BoujeeEnjinia1701/heatmap-node/cad/drawings/HMN-DWG-001.pdf

CONCEPT, NOT FOR FABRICATION | HeatMap Node · github.com/BoujeeEnjinia1701/heatmap-node

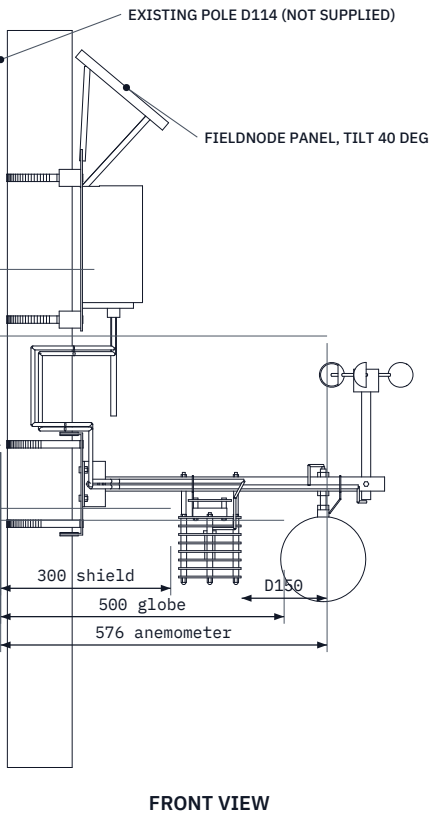
[picture p7: figure]
FRONT VIEW; shield; 500 globe 576 anemometer; EXISTING POLE D114 (NOT SUPPLIED); FIELDNODE PANEL, TILT 40 DEG

Scale 1:12.5; looking at the front (along +Y)

TOP VIEW
Scale 1:12.5; looking down (along -Z)

RIGHT VIEW
Scale 1:12.5; looking at the right side (along -X)

716

290 1300

EL 2668 GLOBE CENTER

EL 2688 T AND RH SENSOR

EL 2800 ARM AXIS

EL 2992 CUP CENTER

EL 3110 FIELDNODE UNDERSIDE

ELEVATIONS ABOVE PAVEMENT

ARM AND PANEL FACE +X (EQUATOR)

ISOMETRIC VIEW
Not to scale; seen from the front right and above, about 30 deg elevation

MAIN DIMENSIONS AND INTERFACES (MM)
Pole D114.3 design case; clamps fit 60 to 200; no drilling
Arm 25 x 25 x 2 Al, 530 long, axis at 2800; reach 668
Saddle: 3 mm sheet channel 120 x 180 x 40, 120 deg V notches, cheeks Shield 8 plates D110 at 15 pitch on 4 M5 rods
Fan 60 x 60 x 15 5 V in 76 sq cowl on the top plate
Globe D150 copper on an M10 hollow hanger tube
Anemometer mast 170 above the arm; cup circle D184
FieldNode core per FND-DWG-001 Rev P3 on printed 120 deg V adapter Lanyards: globe and shield to arm (secondary retention)
Third-angle; front view from -Y; pole on the Z axis; +X to the equator
REV | DESCRIPTION | DATE | BY
P1 | Preliminary GA for TRL 3 (from cad/src/model.py) | 2026-09-25 | AC
P2 | HMN-DDR-002: fan, formed saddle, arm to equator, FieldNode shield | 2026-09-25 | AC
P3 | Layout and labels tidied | 2026-09-25 | AC
P4 | HMN-DDR-003: design for construction (saddle, cheeks, rods, hanger) | 2026-10-01 | AC
P5 | FieldNode core above the arm, leads up the pole (HMN-DEC-001, item 3) | 2026-10-02 | AC
HEATMAP NODE | github.com/BoujeeEnjinia1701/heatmap-node

## General arrangement

DRAWING NO.
HMN-DWG-001

REV
P5

SHEET
1 of 1

SIZE

## ANSI B

SCALE
1:12.5

UNITS
mm
PROJECTION | DATE
2026-10-02

DRAWN
Amish Chadha

MATERIAL / NOTES
Al arm and formed sheet saddle; ASA shield and cowl; copper globe; bought-in parts per bom/bom.csv. PRELIMINARY, NOT FOR FABRICATION
Licensed CERN-OHL-S-2.0 · Design Molecule Lab · designmolecule.com | Generated from cad/src; do not edit by hand
