BoujeeEnjinia1701/heatmap-node/cad/drawings/HMN-DWG-101.pdf

BUILD PLAN SKETCH, PLAN NOT YET BUILT HeatMap Node · github.com/BoujeeEnjinia1701/heatmap-node

FRONT VIEW
Scale 1:5; looking at the front (along +Y)

TOP VIEW
Scale 1:5; looking down (along -Z)

RIGHT VIEW
Scale 1:5; looking at the right side (along -X)

40

120 180

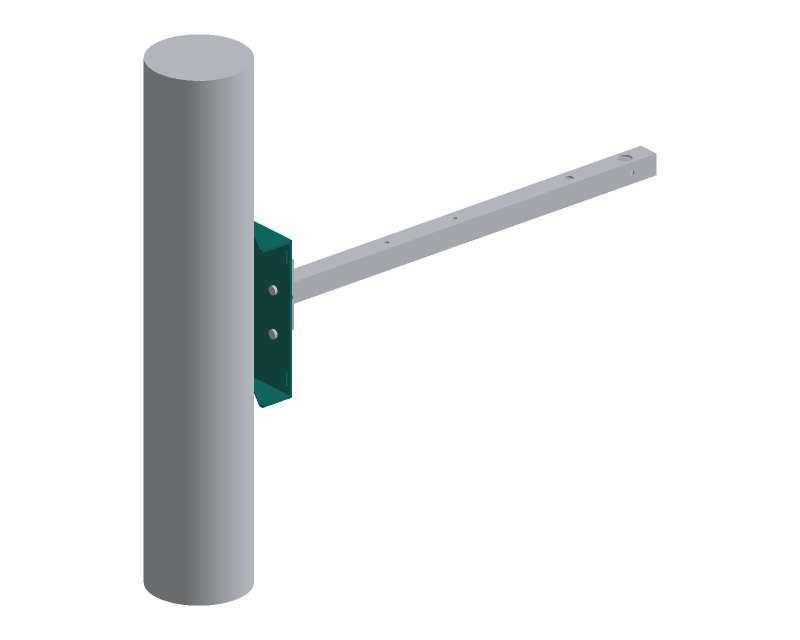
[picture p8: figure]

WHERE IT GOES
This part in colour, its neighbours in grey

HOW TO MAKE IT AND HOW IT FITS
A channel 120 wide, 180 tall and 40 deep, bent from one 3 mm sheet blank. The web is the flat back the arm bears on; the two flanges point at the pole. Blank about 120 x 250 mm; the bending shop sets the length for its bend allowance so the web is 180 outside and each flange stands 40 out.
Before bending, cut a 120 degree V in each end of the blank (the flange): 110.9 wide at the free edge, point 32 in from the edge (8 from the web). Web holes: four 6.6 mm, 35 each side of centre, 25 above and below the middle (65 and 115 up from the bottom edge).
Band slots: four 3 x 16 mm, 55 each side of centre, centred 20 from the top and bottom edges. Chain drill 3 mm and file square.
Bend both flanges 90 degrees the same way, inside radius about 3 mm. Deburr; push rubber edge trim over both V edges (it takes 1.5 mm). Check: on a 114 mm tube both V edges touch the tube through the trim.
REV | DESCRIPTION | DATE | BY
P1 | Making sketch for the prototype build plan | 2026-10-02 | AC
HEATMAP NODE | github.com/BoujeeEnjinia1701/heatmap-node

## HeatMap Node arm saddle: making sketch

DRAWING NO.
HMN-DWG-101

REV
P1

SHEET
1 of 1

SIZE

## ANSI B

SCALE
1:5

UNITS
mm
PROJECTION | DATE
2026-10-02

DRAWN
Amish Chadha

MATERIAL / NOTES
Aluminium sheet 3 mm, 5052-H32
Licensed CERN-OHL-S-2.0 · Design Molecule Lab · designmolecule.com | Generated from cad/src; do not edit by hand
