BoujeeEnjinia1701/heatmap-node/cad/drawings/HMN-DWG-102.pdf

BUILD PLAN SKETCH, PLAN NOT YET BUILT HeatMap Node · github.com/BoujeeEnjinia1701/heatmap-node

FRONT VIEW
Scale 1:1; looking at the front (along +Y)

TOP VIEW
Scale 1:1; looking down (along -Z)

RIGHT VIEW
Scale 1:1; looking at the right side (along -X)

40

40 80

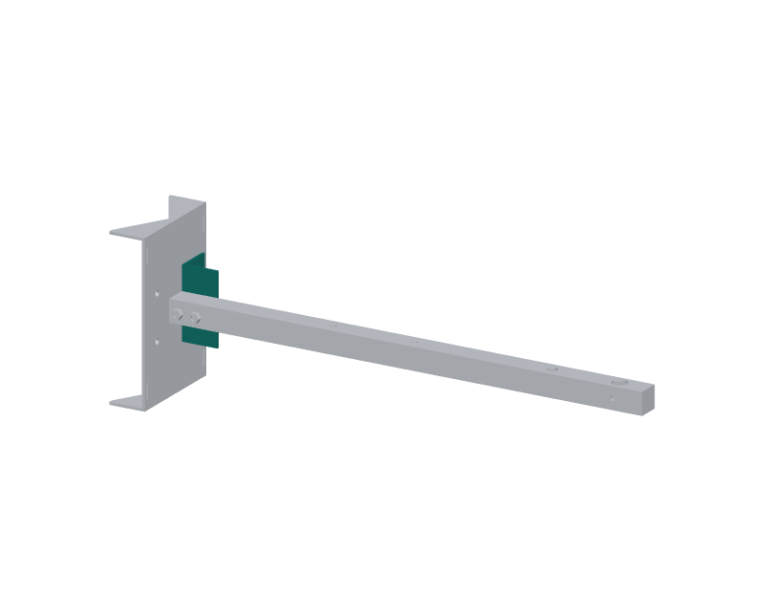
[picture p9: figure]

WHERE IT GOES
This part in colour, its neighbours in grey

HOW TO MAKE IT AND HOW IT FITS
Cut two 80 mm lengths of 40 x 40 x 3 angle; square and deburr the ends. Flat leg (goes on the saddle web): two 6.6 mm holes, 22.5 from the outside corner of the angle, 15 and 65 up from the bottom end.
Upright leg (grips the arm): two 6.6 mm holes at mid-height (40 up),
12 and 32 out from the outside face of the flat leg.
Left and right cheeks are mirror images: clamp the upright legs back to back and drill them together so the holes line up.
Fit: flat leg flat on the web front, the arm between the two upright legs. M6 button-head screws from inside the saddle hold the flat leg; two M6 bolts pass through both cheeks and the arm.
Check: with the arm between them both upright legs touch the arm.
REV | DESCRIPTION | DATE | BY
P1 | Making sketch for the prototype build plan | 2026-10-02 | AC
HEATMAP NODE | github.com/BoujeeEnjinia1701/heatmap-node

## HeatMap Node arm cheek (make 2): making sketch

DRAWING NO.
HMN-DWG-102

REV
P1

SHEET
1 of 1

SIZE

## ANSI B

SCALE
1:1

UNITS
mm
PROJECTION | DATE
2026-10-02

DRAWN
Amish Chadha

MATERIAL / NOTES
Aluminium equal angle 40 x 40 x 3 mm, 6063
Licensed CERN-OHL-S-2.0 · Design Molecule Lab · designmolecule.com | Generated from cad/src; do not edit by hand
