BoujeeEnjinia1701/heatmap-node/cad/drawings/HMN-DWG-103.pdf

BUILD PLAN SKETCH, PLAN NOT YET BUILT HeatMap Node · github.com/BoujeeEnjinia1701/heatmap-node

FRONT VIEW
Scale 1:5; looking at the front (along +Y)

TOP VIEW
Scale 1:5; looking down (along -Z)

RIGHT VIEW
Scale 1:5; looking at the right side (along -X)

530

25 25

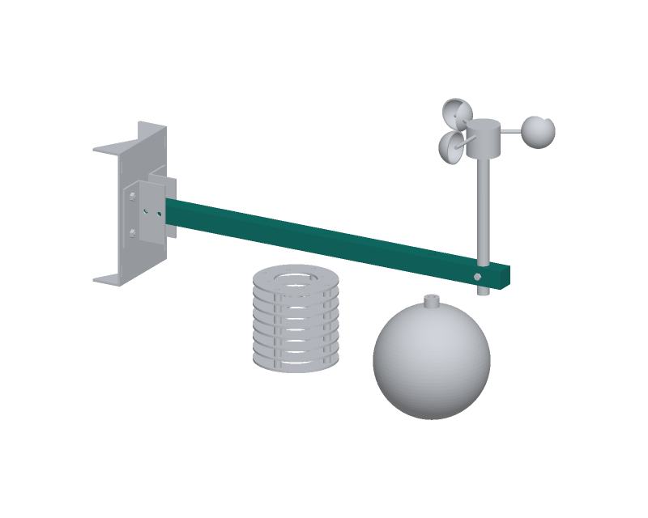
[picture p10: figure]

WHERE IT GOES
This part in colour, its neighbours in grey

HOW TO MAKE IT AND HOW IT FITS
Cut 530 mm of 25 x 25 x 2 tube; square and deburr both ends.
Measure every hole from the root end (the end that bears on the saddle). Through both side walls, on the centre line: 6.6 mm at 12 and 32 (cheek bolts) and 5.5 mm at 500 (anemometer mast cross bolt). Through the top and bottom walls, on the centre line:
5.5 mm at 178.3 and 270.3 (shield rods),
10.5 mm at 424.3 (globe hanger tube),
16.5 mm at 500.0 (anemometer mast; step drill).
Drill each top and bottom pair in one pass on a drill press so they line up; the arm-holes picture in the plan repeats these figures. Push the end plug into the tip and slide the two crush sleeves in from the root end to line up with the cheek bolt holes.
Check: a drill of each hole size passes straight through each pair.
REV | DESCRIPTION | DATE | BY
P1 | Making sketch for the prototype build plan | 2026-10-02 | AC
HEATMAP NODE | github.com/BoujeeEnjinia1701/heatmap-node

## HeatMap Node sensor arm: making sketch

DRAWING NO.
HMN-DWG-103

REV
P1

SHEET
1 of 1

SIZE

## ANSI B

SCALE
1:5

UNITS
mm
PROJECTION | DATE
2026-10-02

DRAWN
Amish Chadha

MATERIAL / NOTES
Aluminium square tube 25 x 25 x 2 mm, 6063
Licensed CERN-OHL-S-2.0 · Design Molecule Lab · designmolecule.com | Generated from cad/src; do not edit by hand
