BoujeeEnjinia1701/heatmap-node/cad/drawings/HMN-DWG-104.pdf

BUILD PLAN SKETCH, PLAN NOT YET BUILT HeatMap Node · github.com/BoujeeEnjinia1701/heatmap-node

FRONT VIEW
Scale 1:2; looking at the front (along +Y)

TOP VIEW
Scale 1:2; looking down (along -Z)

RIGHT VIEW
Scale 1:2; looking at the right side (along -X)

110

110 3

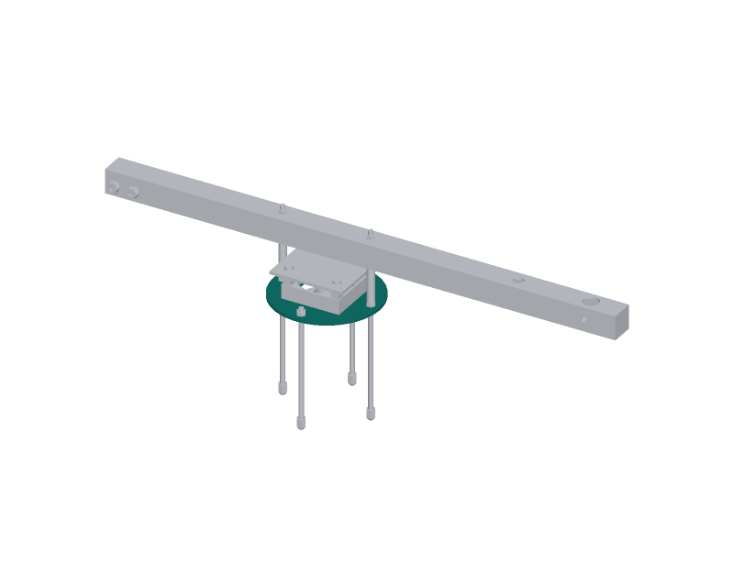
[picture p11: figure]

WHERE IT GOES
This part in colour, its neighbours in grey

HOW TO MAKE IT AND HOW IT FITS
Print one, flat, 110 mm across and 3 mm thick, in white ASA, 4 walls, 40 % infill or more, in an enclosed printer.
Centre hole 56 mm: the fan draws air up through it.
Four 5.5 mm rod holes on a 92 mm circle, 90 degrees apart
(46 from the centre); two of them line up with the arm. Four 4.4 mm fan screw holes on a 50 mm square, centred.
The rod holes sit on the square's centre lines, the fan holes
on its diagonals.
Fit: the fan sits flat on top over the centre hole; the cowl stands on
the fan; four M4 x 40 screws go through cowl, fan and plate, nuts below. Nuts on the four rods clamp this plate down onto the stack.
Check: the fan's corner holes line up with the four 4.4 mm holes.
REV | DESCRIPTION | DATE | BY
P1 | Making sketch for the prototype build plan | 2026-10-02 | AC
HEATMAP NODE | github.com/BoujeeEnjinia1701/heatmap-node

## HeatMap Node top shield plate: making sketch

DRAWING NO.
HMN-DWG-104

REV
P1

SHEET
1 of 1

SIZE

## ANSI B

SCALE
1:2

UNITS
mm
PROJECTION | DATE
2026-10-02

DRAWN
Amish Chadha

MATERIAL / NOTES
UV-stable white ASA, 3D printed
Licensed CERN-OHL-S-2.0 · Design Molecule Lab · designmolecule.com | Generated from cad/src; do not edit by hand
