BoujeeEnjinia1701/heatmap-node/cad/drawings/HMN-DWG-105.pdf

BUILD PLAN SKETCH, PLAN NOT YET BUILT HeatMap Node · github.com/BoujeeEnjinia1701/heatmap-node

FRONT VIEW
Scale 1:2; looking at the front (along +Y)

TOP VIEW
Scale 1:2; looking down (along -Z)

RIGHT VIEW
Scale 1:2; looking at the right side (along -X)

110

110 15

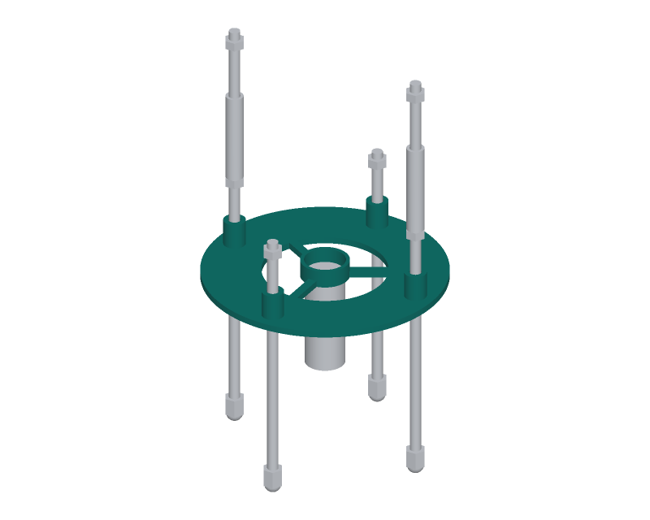
[picture p12: figure]

WHERE IT GOES
This part in colour, its neighbours in grey

HOW TO MAKE IT AND HOW IT FITS
Print seven ring plates flat, bosses up: 110 mm across, 3 mm thick, with a 56 mm centre hole. Print six without the hub.
Four bosses 10 mm across and 12 mm tall stand on each ring around 5.5 mm rod holes on a 92 mm circle. Each boss carries the plate above, so the plates sit 15 mm apart with 12 mm air gaps.
The seventh ring (the third plate from the top) also has a hub 22 mm across and 8 mm tall on three 4 mm spokes; its 18.5 mm bore holds the sensor capsule. Add a 2.5 mm side hole in the hub and tap or thread-form it M3 for a nylon set screw.
Fit: the rods pass through the bosses; nothing is glued.
Check: eight plates stack 108 mm tall on the rods, gaps even.
REV | DESCRIPTION | DATE | BY
P1 | Making sketch for the prototype build plan | 2026-10-02 | AC
HEATMAP NODE | github.com/BoujeeEnjinia1701/heatmap-node

## HeatMap Node ring plates (make 7; one with the sensor hub): making sketch

DRAWING NO.
HMN-DWG-105

REV
P1

SHEET
1 of 1

SIZE

## ANSI B

SCALE
1:2

UNITS
mm
PROJECTION | DATE
2026-10-02

DRAWN
Amish Chadha

MATERIAL / NOTES
UV-stable white ASA, 3D printed
Licensed CERN-OHL-S-2.0 · Design Molecule Lab · designmolecule.com | Generated from cad/src; do not edit by hand
