BoujeeEnjinia1701/heatmap-node/cad/drawings/HMN-DWG-106.pdf

BUILD PLAN SKETCH, PLAN NOT YET BUILT HeatMap Node · github.com/BoujeeEnjinia1701/heatmap-node

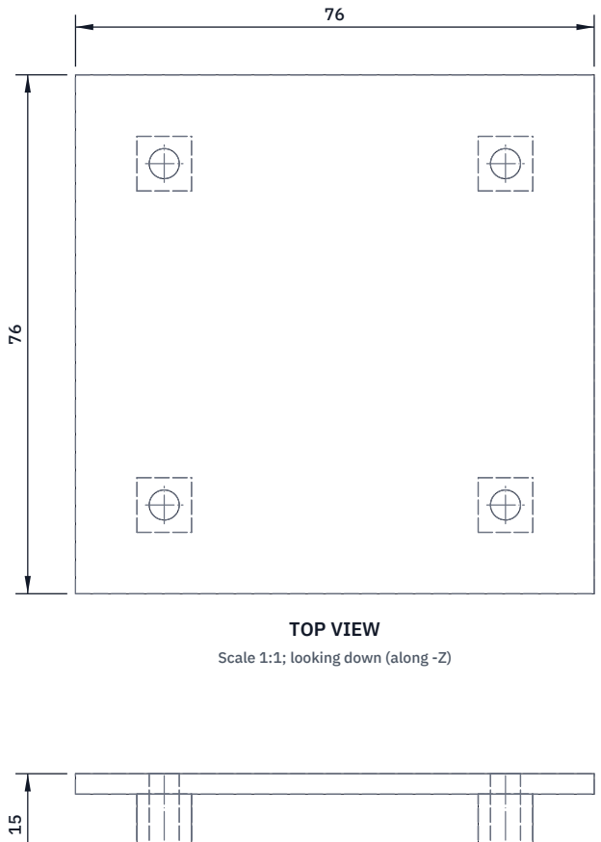
[picture p13: figure]
TOP VIEW; Scale 1:1; looking down (along -Z)

FRONT VIEW
Scale 1:1; looking at the front (along +Y)

RIGHT VIEW
Scale 1:1; looking at the right side (along -X)

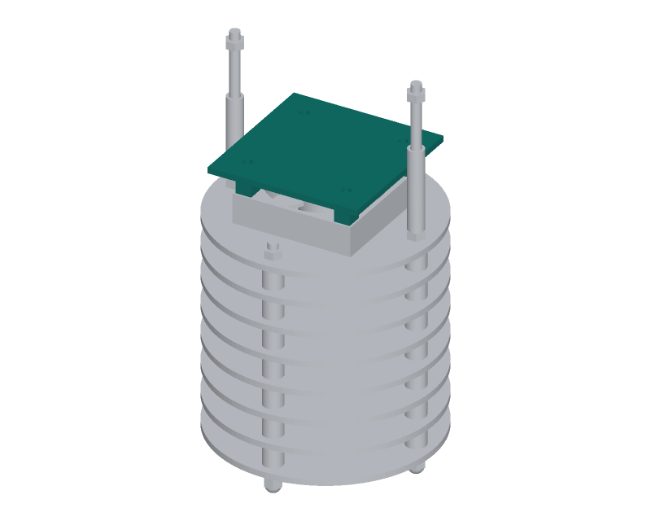
[picture p14: figure]

WHERE IT GOES
This part in colour, its neighbours in grey

HOW TO MAKE IT AND HOW IT FITS
Print one, lid down: a lid 76 x 76 x 3 mm on four legs 8 x 8 mm. The legs stand on the fan's four corners, on a 50 mm square, and lift the lid 12 mm above the fan so the air leaves sideways. Overall height from the top plate is 30 mm (fan 15, legs 12, lid 3). A 4.4 mm hole runs down through each leg and the lid.
Fit: four M4 x 40 pan-head screws from the top of the lid, through the legs, the fan's corner holes and the top plate, with nuts under the plate. Tighten lightly: the fan frame is plastic.
The lid edge stays 4 mm or more clear of the rods and spacers. Check: the lid sits level and the fan spins freely by hand.
REV | DESCRIPTION | DATE | BY
P1 | Making sketch for the prototype build plan | 2026-10-02 | AC
HEATMAP NODE | github.com/BoujeeEnjinia1701/heatmap-node

## HeatMap Node fan cowl: making sketch

DRAWING NO.
HMN-DWG-106

REV
P1

SHEET
1 of 1

SIZE

## ANSI B

SCALE
1:1

UNITS
mm
PROJECTION | DATE
2026-10-02

DRAWN
Amish Chadha

MATERIAL / NOTES
UV-stable white ASA, 3D printed
Licensed CERN-OHL-S-2.0 · Design Molecule Lab · designmolecule.com | Generated from cad/src; do not edit by hand
