BoujeeEnjinia1701/heatmap-node/cad/drawings/HMN-DWG-107.pdf

BUILD PLAN SKETCH, PLAN NOT YET BUILT HeatMap Node · github.com/BoujeeEnjinia1701/heatmap-node

FRONT VIEW
Scale 1:1; looking at the front (along +Y)

TOP VIEW
Scale 1:1; looking down (along -Z)

RIGHT VIEW
Scale 1:1; looking at the right side (along -X)

110

38 30

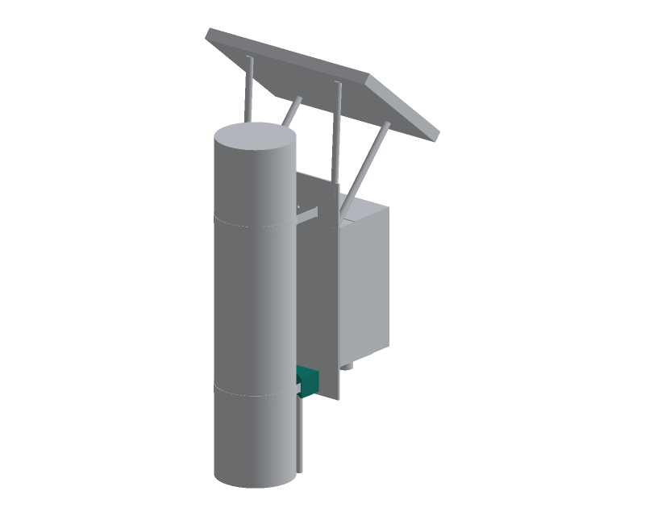
[picture p15: figure]

WHERE IT GOES
This part in colour, its neighbours in grey

HOW TO MAKE IT AND HOW IT FITS
Print two, standing on the 110 x 38 mm face, 100 % infill, 5 walls. Block 110 wide, 30 tall and 38 deep with a 120 degree V across its whole width: point 31.8 in from the pole face, 6.2 from the back.
Two band slots 3.5 x 16 mm right through, front to back, 51 each side of centre, centred on the height; they line up with the slots in
the FieldNode back plate.
Two holes for M4 brass heat-set inserts in the flat back face, 18 each side of centre, centred on the height, 8 deep; press the inserts in with a soldering iron, flush.
Fit: the flat back sits on the back of the FieldNode back plate in place of FieldNode's own V-blocks, held by its M4 countersunk screws. Check: poles of 60, 114 and 200 mm each touch both V faces.
REV | DESCRIPTION | DATE | BY
P1 | Making sketch for the prototype build plan | 2026-10-02 | AC
HEATMAP NODE | github.com/BoujeeEnjinia1701/heatmap-node

## HeatMap Node pole adapter V-block (make 2): making sketch

DRAWING NO.
HMN-DWG-107

REV
P1

SHEET
1 of 1

SIZE

## ANSI B

SCALE
1:1

UNITS
mm
PROJECTION | DATE
2026-10-02

DRAWN
Amish Chadha

MATERIAL / NOTES
ASA, 3D printed at 100 % infill
Licensed CERN-OHL-S-2.0 · Design Molecule Lab · designmolecule.com | Generated from cad/src; do not edit by hand
