BoujeeEnjinia1701/heatmap-node/cad/drawings/HMN-DWG-001.png

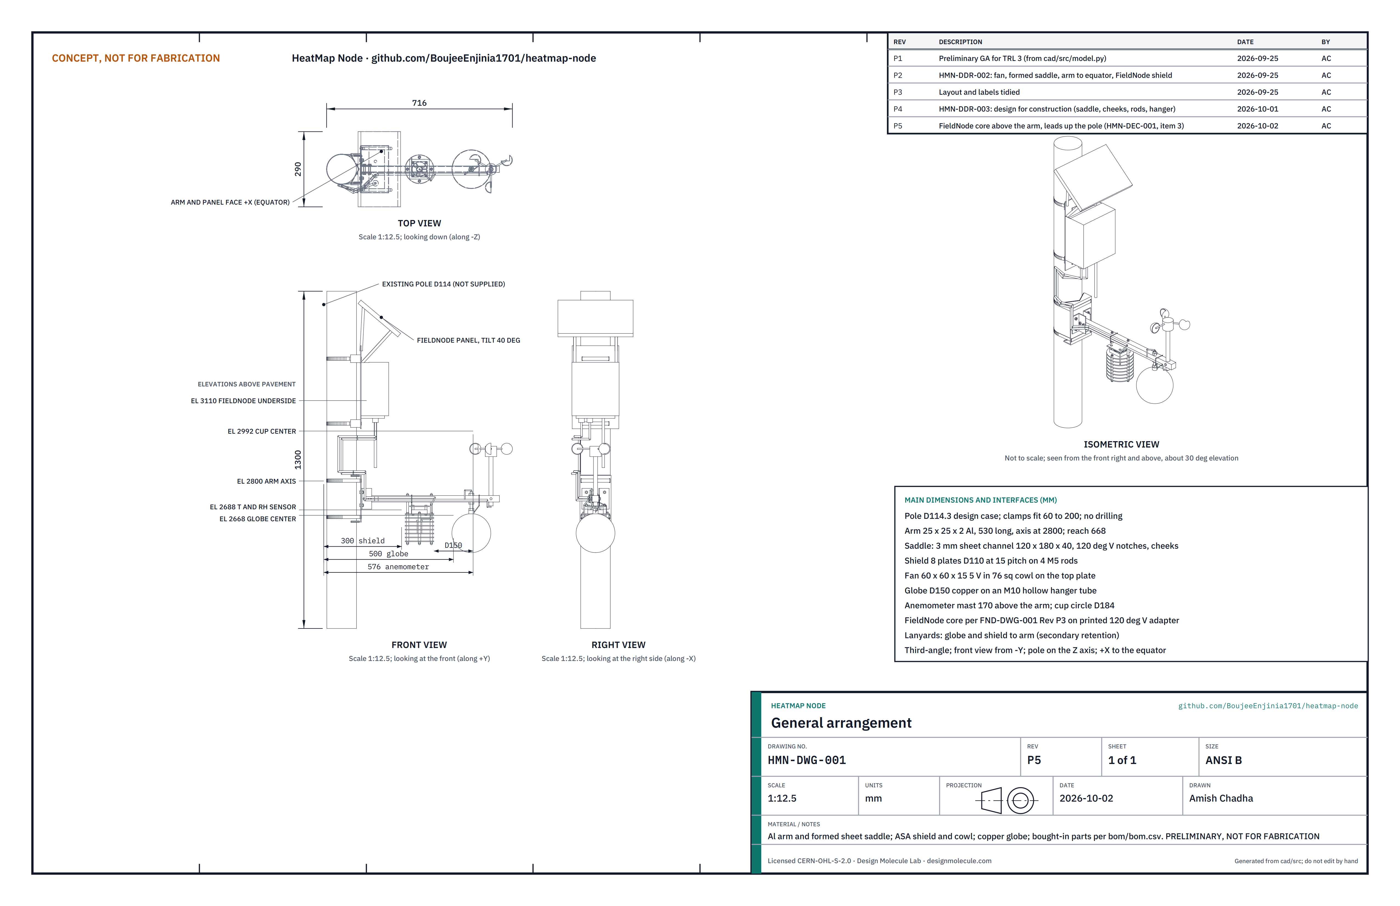
cad/drawings/HMN-DWG-001.png
