BoujeeEnjinia1701/heatmap-node/media/card.png

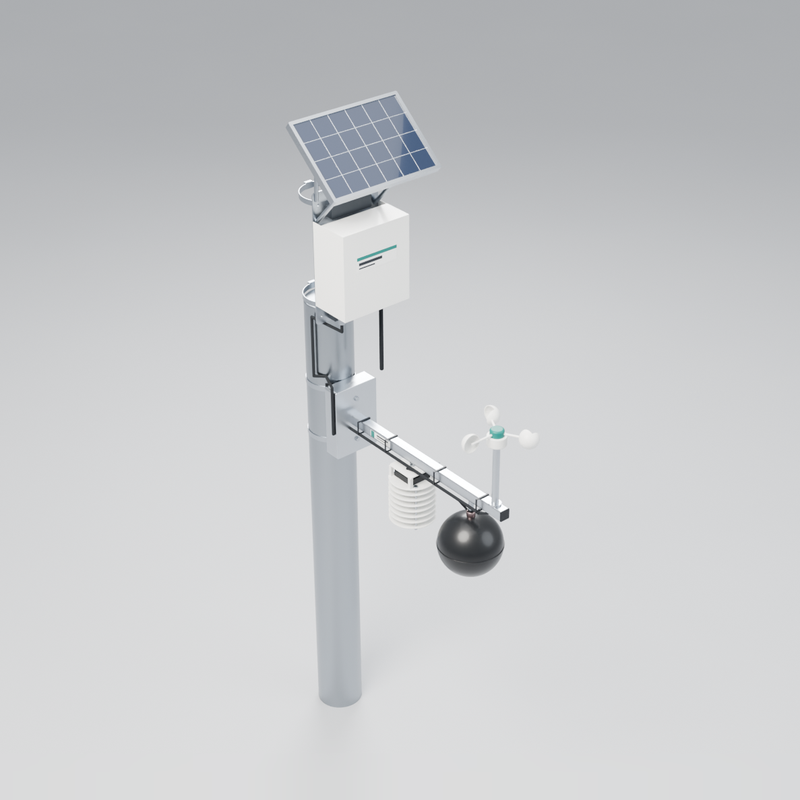
media/card.png
