BoujeeEnjinia1701/heatmap-node/media/render-detail.png

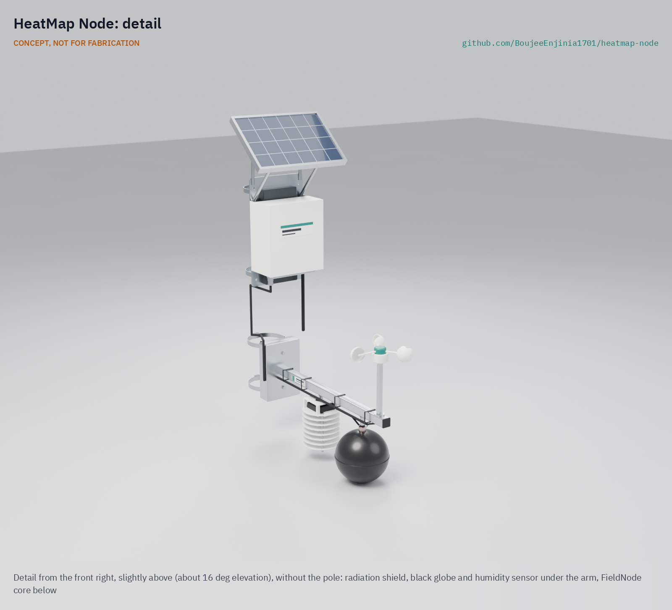
media/render-detail.png
