BoujeeEnjinia1701/heatmap-node/media/render-exploded.png

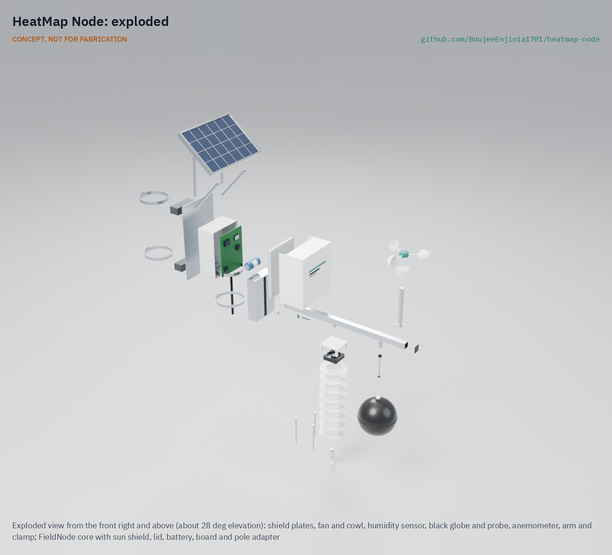
media/render-exploded.png
