BoujeeEnjinia1701/heatmap-node/media/social-preview.png

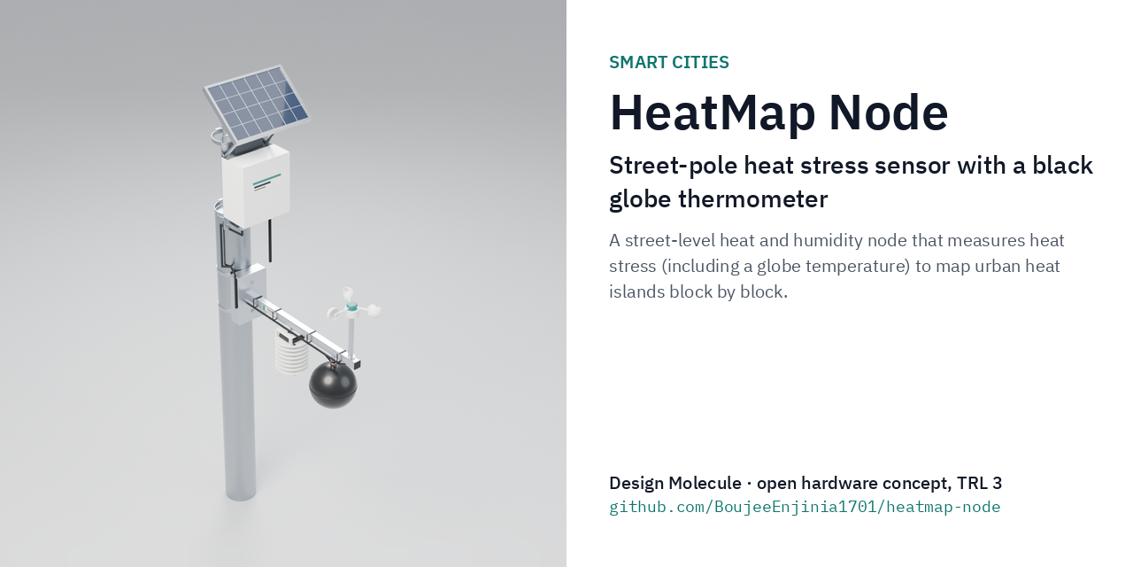
media/social-preview.png
